IshikawaRasoto/integration-workshop-3/electronics/kicad-5/documentation/aht10_breakout/images/footprint.png

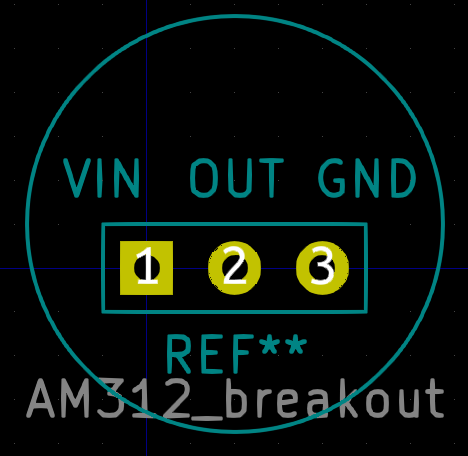
electronics/kicad-5/documentation/aht10_breakout/images/footprint.png
