IshikawaRasoto/integration-workshop-3/electronics/kicad-5/documentation/esp32_devkit_v1_doit/images/3d_top.png

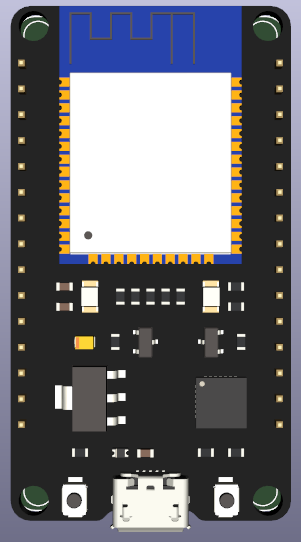
electronics/kicad-5/documentation/esp32_devkit_v1_doit/images/3d_top.png
