IshikawaRasoto/integration-workshop-3/electronics/kicad-5/documentation/esp32_devkit_v1_doit/images/symbol.png

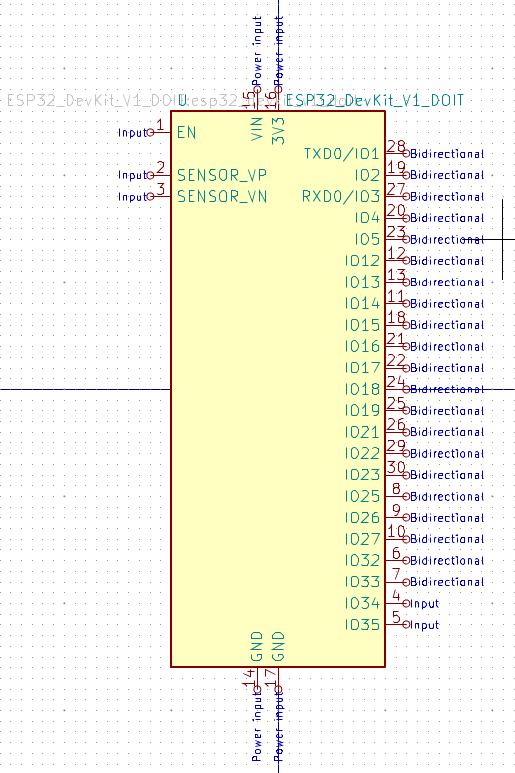
electronics/kicad-5/documentation/esp32_devkit_v1_doit/images/symbol.png
