IshikawaRasoto/integration-workshop-3/electronics/kicad-5/documentation/kf301_5.0/images/3d_view.png

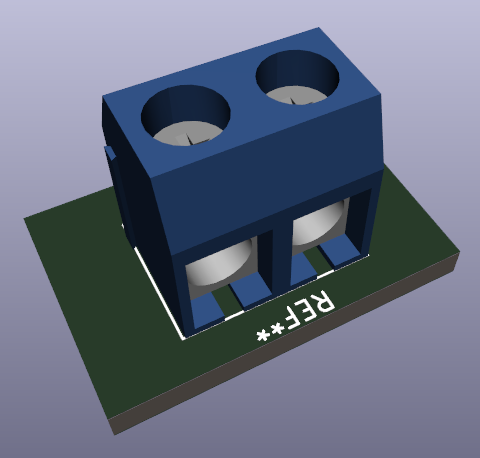
electronics/kicad-5/documentation/kf301_5.0/images/3d_view.png
