IshikawaRasoto/integration-workshop-3/electronics/kicad-5/documentation/kf301_5.0/images/picture.jpg

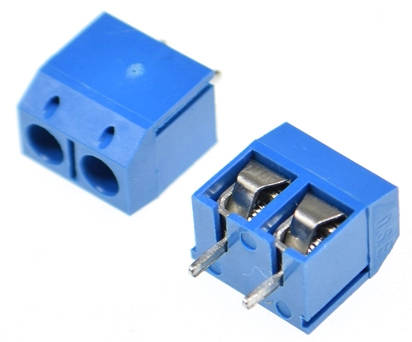
electronics/kicad-5/documentation/kf301_5.0/images/picture.jpg
