IshikawaRasoto/integration-workshop-3/electronics/melody/melody.kicad_pcb

## KiCad design electronics/melody/melody.kicad_pcb (2025-05-14)

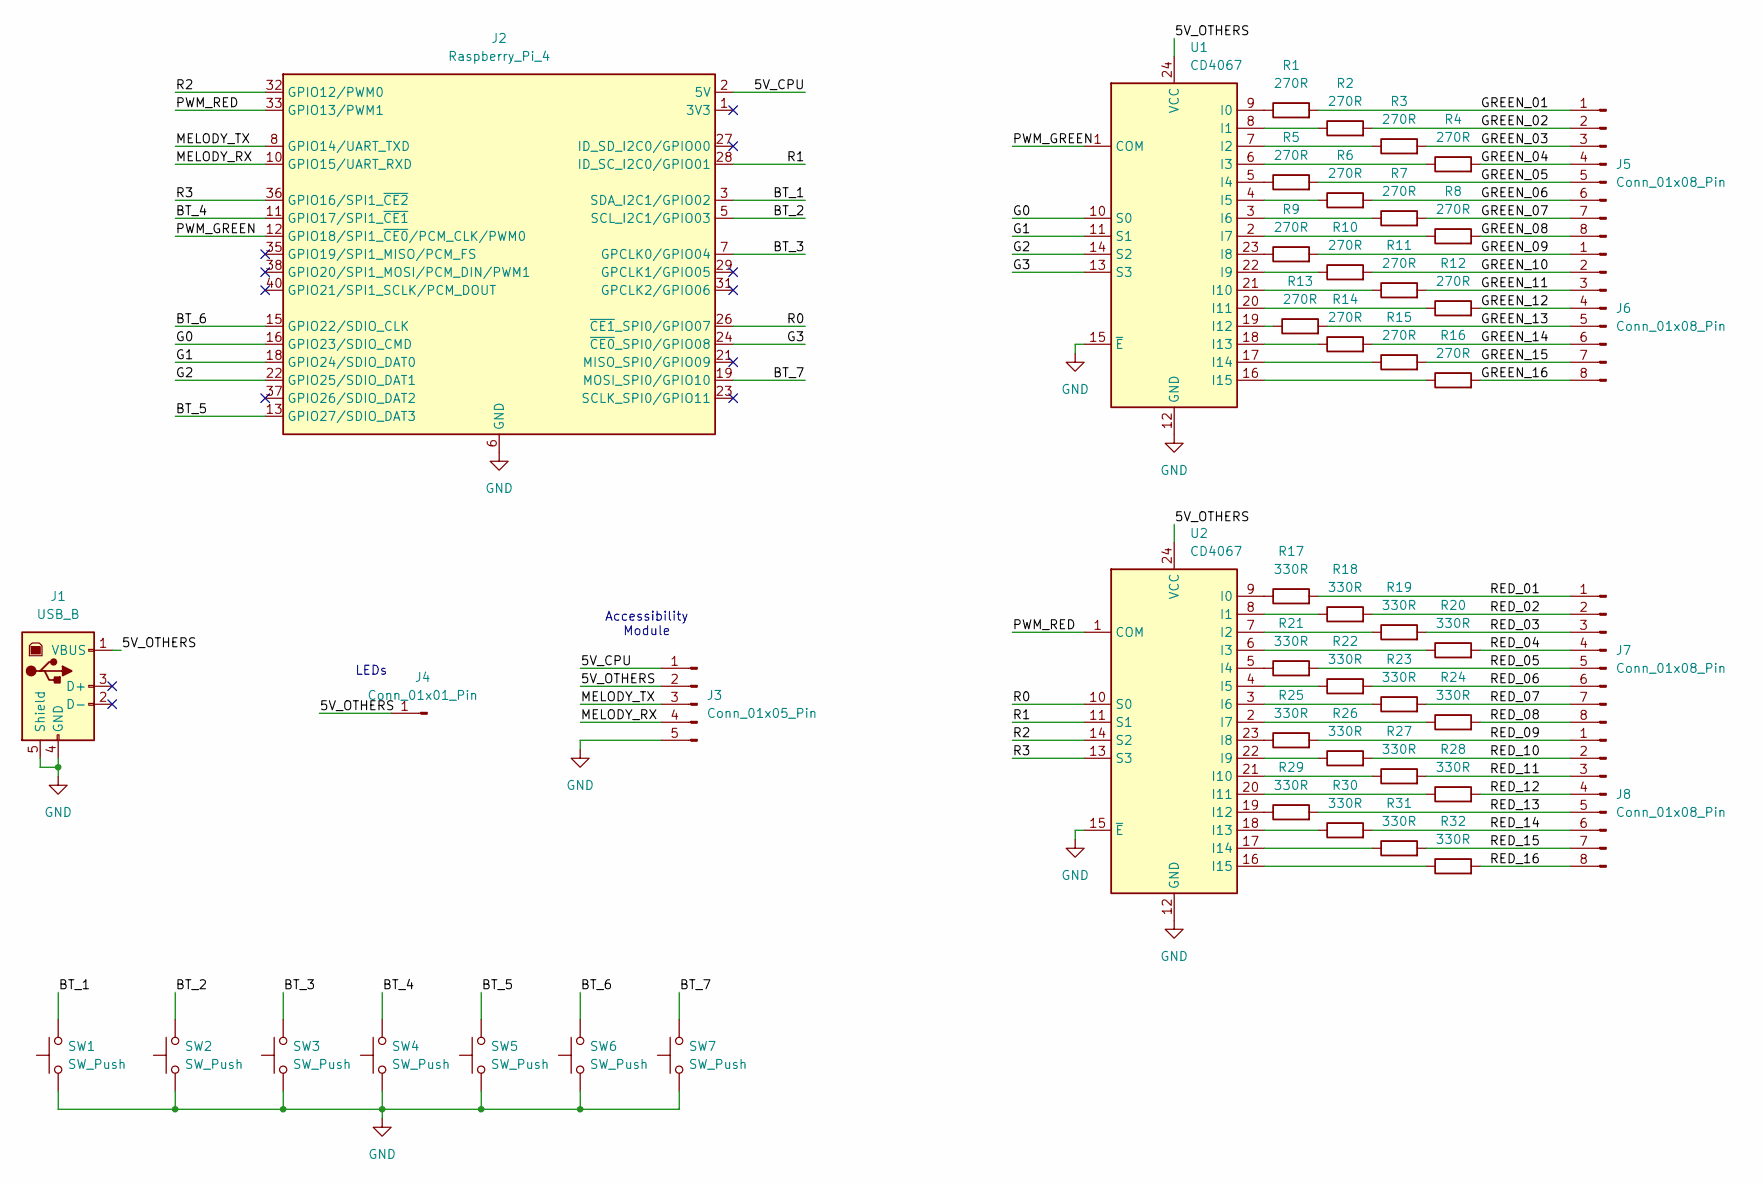
[picture p17: schematic melody.kicad_sch]

Parts:
J1: USB_B; USB_B_TE_5787834_Vertical
J2: Raspberry_Pi_4; PinSocket_2x20_P2.54mm_Vertical
J3: Conn_01x05_Pin; PinHeader_1x05_P2.54mm_Vertical
J4: Conn_01x01_Pin; PinSocket_1x01_P2.54mm_Vertical
J5, J6, J7, J8: Conn_01x08_Pin; PinHeader_1x08_P2.54mm_Vertical
R1, R2, R3, R4, R5, R6, R7, R8, R9, R10, R11, R12, R13, R14, R15, R16: 270R; R_Axial_DIN0204_L3.6mm_D1.6mm_P7.62mm_Horizontal
R17, R18, R19, R20, R21, R22, R23, R24, R25, R26, R27, R28, R29, R30, R31, R32: 330R; R_Axial_DIN0204_L3.6mm_D1.6mm_P7.62mm_Horizontal
SW1, SW2, SW3, SW4, SW5, SW6, SW7: SW_Push; PinHeader_1x02_P2.54mm_Vertical
U1, U2: CD4067; DIP-24_W15.24mm_LongPads

Connections:
/5V_CPU: J2.2 (5V), J2.4 (5V), J3.1
/5V_OTHERS: J1.1 (VBUS), J3.2, J4.1, U1.24 (VCC), U2.24 (VCC)
/BT_1: J2.3 (SDA_I2C1/GPIO02), SW1.2
/BT_2: J2.5 (SCL_I2C1/GPIO03), SW2.2
/BT_3: J2.7 (GPCLK0/GPIO04), SW3.2
/BT_4: J2.11 (GPIO17/SPI1_~CE1), SW4.2
/BT_5: J2.13 (GPIO27/SDIO_DAT3), SW5.2
/BT_6: J2.15 (GPIO22/SDIO_CLK), SW6.2
/BT_7: J2.19 (MOSI_SPI0/GPIO10), SW7.2
/G0: J2.16 (GPIO23/SDIO_CMD), U1.10 (S0)
/G1: J2.18 (GPIO24/SDIO_DAT0), U1.11 (S1)
/G2: J2.22 (GPIO25/SDIO_DAT1), U1.14 (S2)
/G3: J2.24 (~CE0_SPI0/GPIO08), U1.13 (S3)
/GREEN_01: J5.1, R1.2
/GREEN_02: J5.2, R2.2
/GREEN_03: J5.3, R3.2
/GREEN_04: J5.4, R4.2
/GREEN_05: J5.5, R5.2
/GREEN_06: J5.6, R6.2
/GREEN_07: J5.7, R7.2
/GREEN_08: J5.8, R8.2
/GREEN_09: J6.1, R9.2
/GREEN_10: J6.2, R10.2
/GREEN_11: J6.3, R11.2
/GREEN_12: J6.4, R12.2
/GREEN_13: J6.5, R13.2
/GREEN_14: J6.6, R14.2
/GREEN_15: J6.7, R15.2
/GREEN_16: J6.8, R16.2
/MELODY_RX: J2.10 (GPIO15/UART_RXD), J3.4
/MELODY_TX: J2.8 (GPIO14/UART_TXD), J3.3
/PWM_GREEN: J2.12 (GPIO18/SPI1_~CE0/PCM_CLK/PWM0), U1.1 (COM)
/PWM_RED: J2.33 (GPIO13/PWM1), U2.1 (COM)
/R0: J2.26 (~CE1_SPI0/GPIO07), U2.10 (S0)
/R1: J2.28 (ID_SC_I2C0/GPIO01), U2.11 (S1)
/R2: J2.32 (GPIO12/PWM0), U2.14 (S2)
/R3: J2.36 (GPIO16/SPI1_~CE2), U2.13 (S3)
/RED_01: J7.1, R17.2
/RED_02: J7.2, R18.2
/RED_03: J7.3, R19.2
/RED_04: J7.4, R20.2
/RED_05: J7.5, R21.2
/RED_06: J7.6, R22.2
/RED_07: J7.7, R23.2
/RED_08: J7.8, R24.2
/RED_09: J8.1, R25.2
/RED_10: J8.2, R26.2
/RED_11: J8.3, R27.2
/RED_12: J8.4, R28.2
/RED_13: J8.5, R29.2
/RED_14: J8.6, R30.2
/RED_15: J8.7, R31.2
/RED_16: J8.8, R32.2
GND: J1.4 (GND), J1.5 (Shield), J2.6 (GND), J2.9 (GND), J2.14 (GND), J2.20 (GND), J2.25 (GND), J2.30 (GND), J2.34 (GND), J2.39 (GND), J3.5, SW1.1, SW2.1, SW3.1, SW4.1, SW5.1, SW6.1, SW7.1, U1.12 (GND), U1.15 (~E), U2.12 (GND), U2.15 (~E)
unnamed: R1.1, U1.9 (I0)
unnamed: R2.1, U1.8 (I1)
unnamed: R3.1, U1.7 (I2)
unnamed: R4.1, U1.6 (I3)
unnamed: R5.1, U1.5 (I4)
unnamed: R6.1, U1.4 (I5)
unnamed: R7.1, U1.3 (I6)
unnamed: R8.1, U1.2 (I7)
unnamed: R9.1, U1.23 (I8)
unnamed: R10.1, U1.22 (I9)
unnamed: R11.1, U1.21 (I10)
unnamed: R12.1, U1.20 (I11)
unnamed: R13.1, U1.19 (I12)
unnamed: R14.1, U1.18 (I13)
unnamed: R15.1, U1.17 (I14)
unnamed: R16.1, U1.16 (I15)
unnamed: R17.1, U2.9 (I0)
unnamed: R18.1, U2.8 (I1)
unnamed: R19.1, U2.7 (I2)
unnamed: R20.1, U2.6 (I3)
unnamed: R21.1, U2.5 (I4)
unnamed: R22.1, U2.4 (I5)
unnamed: R23.1, U2.3 (I6)
unnamed: R24.1, U2.2 (I7)
unnamed: R25.1, U2.23 (I8)
unnamed: R26.1, U2.22 (I9)
unnamed: R27.1, U2.21 (I10)
unnamed: R28.1, U2.20 (I11)
unnamed: R29.1, U2.19 (I12)
unnamed: R30.1, U2.18 (I13)
unnamed: R31.1, U2.17 (I14)
unnamed: R32.1, U2.16 (I15)

Notes on the sheet:
LEDs
Accessibility Module

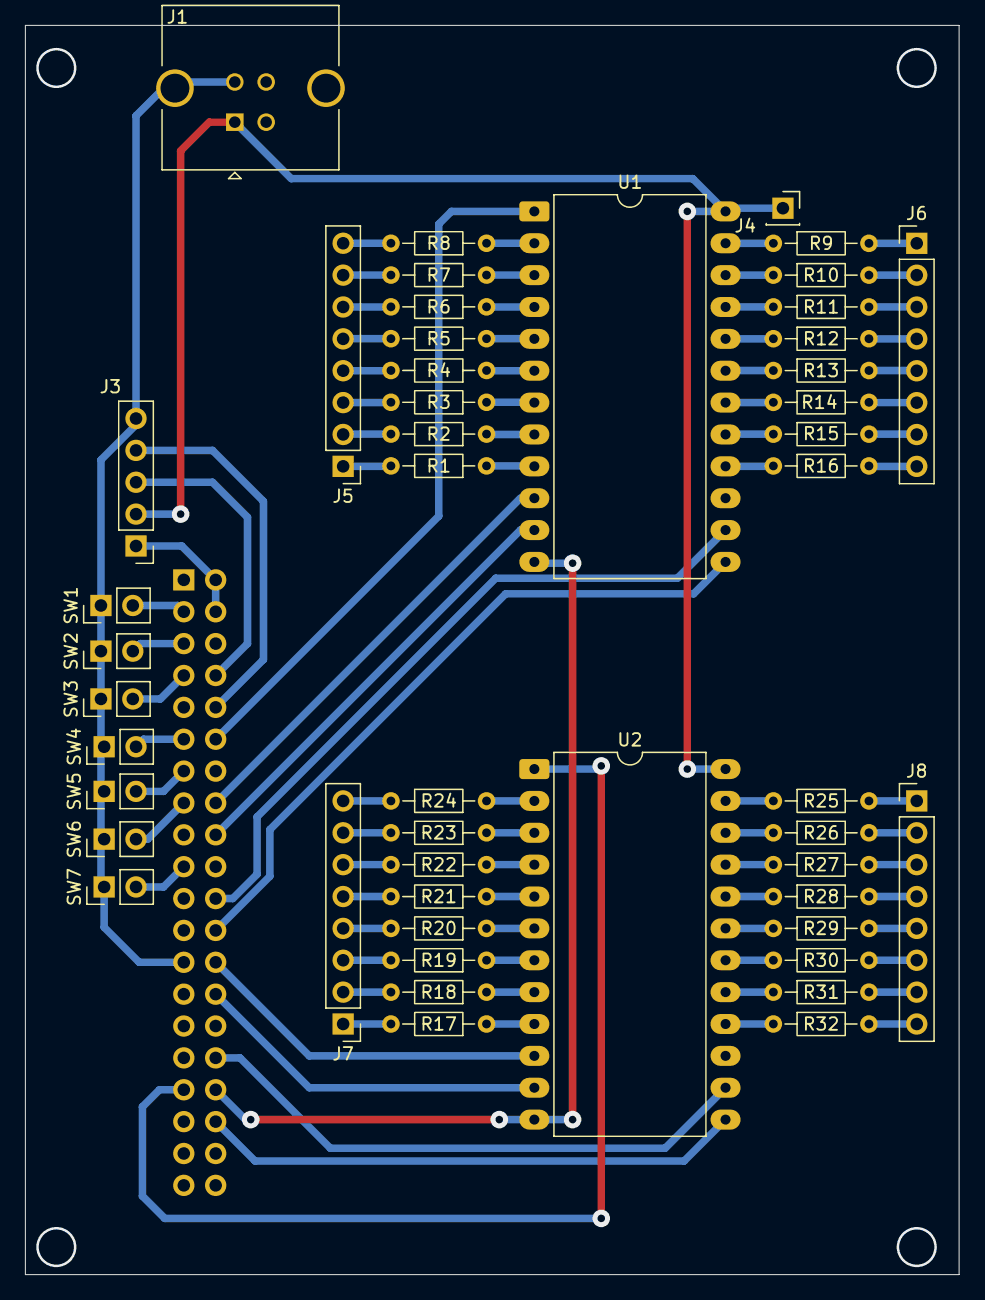
[picture p18: board melody.kicad_pcb from above]

Board: 2 copper layers, 74.4 x 99.6 mm, 49 parts (1 on the bottom side), 86 nets.
