IshikawaRasoto/integration-workshop-3/electronics/accessibility_module/accessibility_module.kicad_pcb

## KiCad design electronics/accessibility_module/accessibility_module.kicad_pcb (2025-05-14)

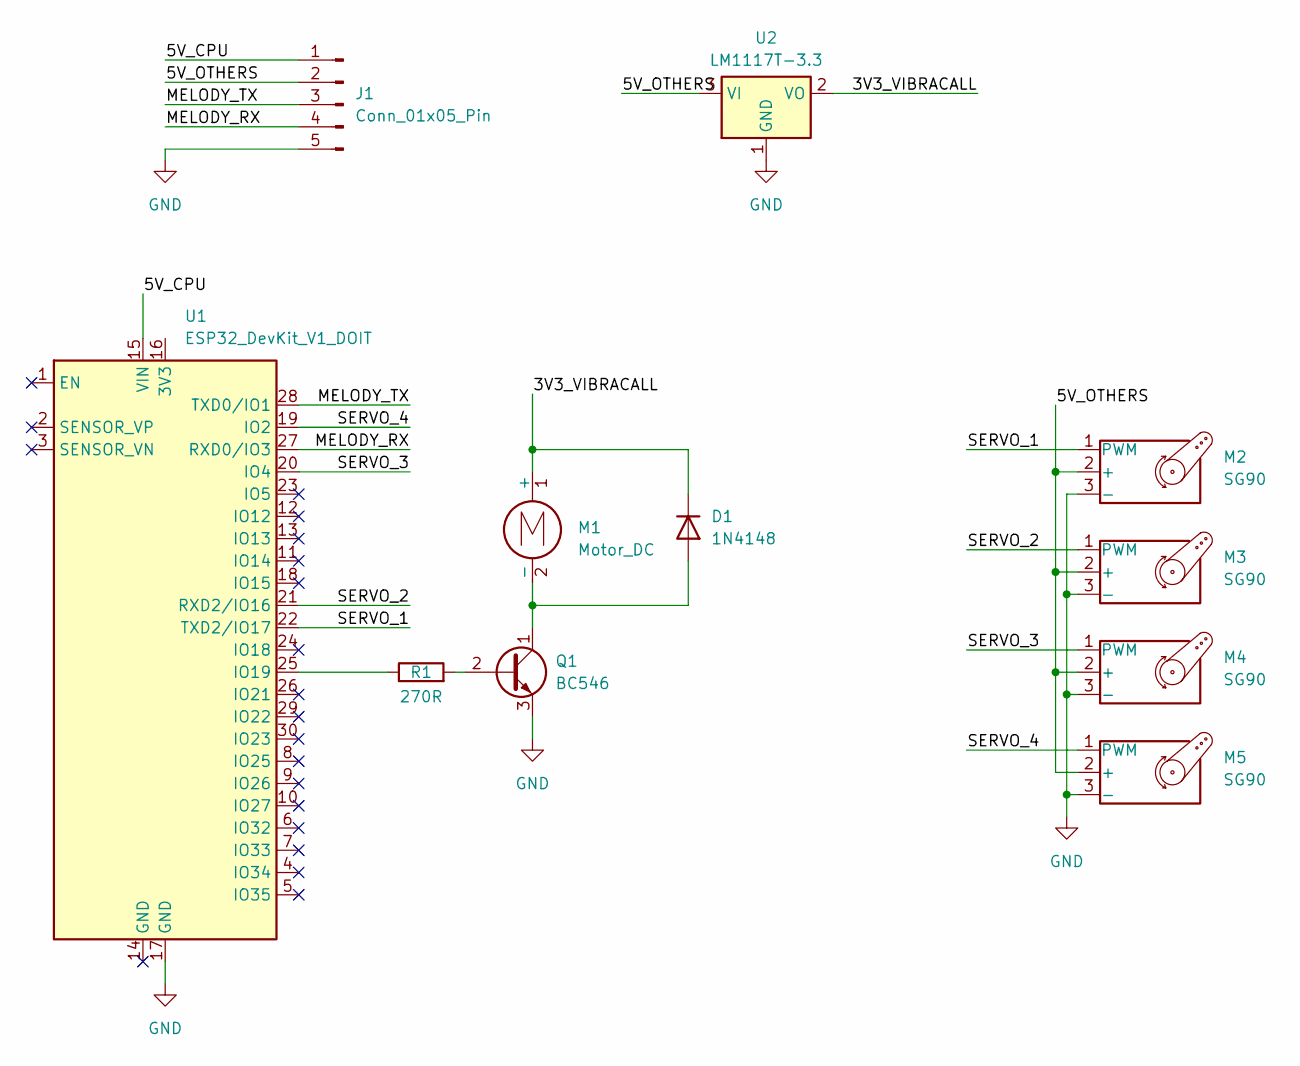
[picture p19: schematic accessibility_module.kicad_sch, Accessibility Module]

Parts:
D1: 1N4148; D_DO-35_SOD27_P7.62mm_Horizontal
J1: Conn_01x05_Pin; PinHeader_1x05_P2.54mm_Vertical
M1: Motor_DC; PinHeader_1x02_P2.54mm_Vertical
M2, M3, M4, M5: SG90; PinHeader_1x03_P2.54mm_Vertical
Q1: BC546; TO-92_Inline
R1: 270R; R_Axial_DIN0204_L3.6mm_D1.6mm_P7.62mm_Horizontal
U1: ESP32_DevKit_V1_DOIT; esp32_devkit_v1_doit
U2: LM1117T-3.3; TO-220-3_Vertical

Connections:
/3V3_VIBRACALL: D1.1 (K), M1.1 (+), U2.2 (VO)
/5V_CPU: J1.1, U1.15 (VIN)
/5V_OTHERS: J1.2, M2.2 (+), M3.2 (+), M4.2 (+), M5.2 (+), U2.3 (VI)
/MELODY_RX: J1.4, U1.27 (RXD0/IO3)
/MELODY_TX: J1.3, U1.28 (TXD0/IO1)
/SERVO_1: M2.1 (PWM), U1.22 (TXD2/IO17)
/SERVO_2: M3.1 (PWM), U1.21 (RXD2/IO16)
/SERVO_3: M4.1 (PWM), U1.20 (IO4)
/SERVO_4: M5.1 (PWM), U1.19 (IO2)
GND: J1.5, M2.3 (-), M3.3 (-), M4.3 (-), M5.3 (-), Q1.3 (E), U1.17 (GND), U2.1 (GND)
unnamed: D1.2 (A), M1.2 (-), Q1.1 (C)
unnamed: Q1.2 (B), R1.2
unnamed: R1.1, U1.25 (IO19)

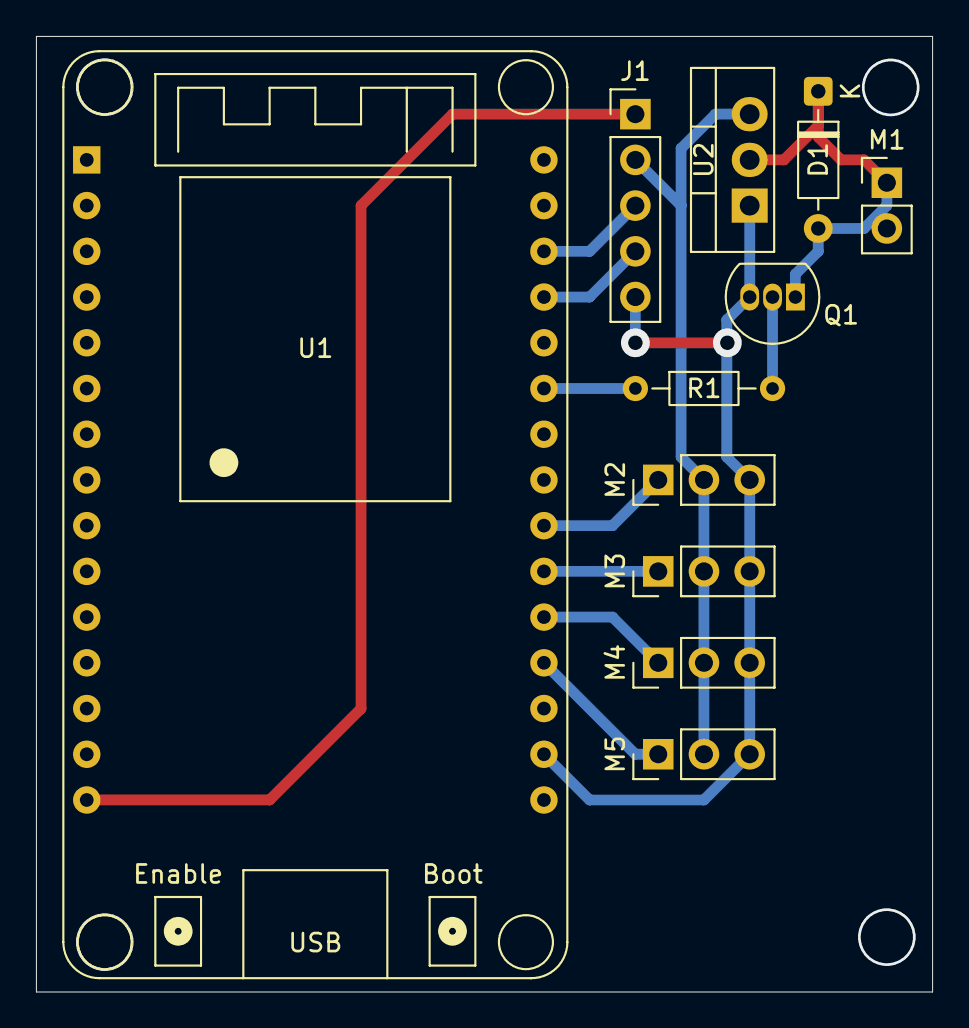
[picture p20: board accessibility_module.kicad_pcb from above]

Board: 2 copper layers, 49.8 x 53.1 mm, 11 parts (0 on the bottom side), 13 nets.
