IshikawaRasoto/integration-workshop-3/backend/core/utils.py

# Melodies

ODE_ALEGRIA = [
    ("C5#", "quarter"), ("C5#", "quarter"), ("D5", "quarter"), ("E5", "quarter"),
    ("E5", "quarter"), ("D5", "quarter"), ("C5#", "quarter"), ("B4", "quarter"),
    ("A4", "half"), ("R", ""), ("B4", "quarter"), ("C5#", "quarter"),
    ("C5#", "half"), ("R", ""), ("B4", "half"), ("R", "")

]

CANON_IN_D = [
    ("D5", "half"), ("R", ""), ("A4", "half"), ("R", ""),
    ("B4", "half"), ("R", ""), ("F4#", "half"), ("R", ""),
    ("G4", "half"), ("R", ""), ("D4", "half"), ("R", ""),
    ("G4", "half"), ("R", ""), ("A4", "half"), ("R", "")
]

OVELHA_PRETA = [
    ("G4", "quarter"), ("G4", "quarter"), ("D5", "quarter"), ("D5", "quarter"),
    ("E5", "quarter"), ("E5", "quarter"), ("D5", "half"),    ("R", ""),
    ("C5", "quarter"), ("C5", "quarter"), ("B4", "quarter"), ("B4", "quarter"),
    ("A4", "quarter"), ("A4", "quarter"), ("G4", "half"),    ("R", "")
]


# Frequencies for 12 chromatic notes
note_freqs = {
    'C1': 32.70, 'C1#': 34.65, 'D1b': 34.65, 'D1': 36.71, 'D1#': 38.89, 'E1b': 38.89, 'E1': 41.20,
    'F1': 43.65, 'F1#': 46.25, 'G1b': 46.25, 'G1': 49.00, 'G1#': 51.91, 'A1b': 51.91, 'A1': 55.00,
    'A1#': 58.27, 'B1b': 58.27, 'B1': 61.74,
    'C2': 65.41, 'C2#': 69.30, 'D2b': 69.30, 'D2': 73.42, 'D2#': 77.78, 'E2b': 77.78, 'E2': 82.41,
    'F2': 87.31, 'F2#': 92.50, 'G2b': 92.50, 'G2': 98.00, 'G2#': 103.83, 'A2b': 103.83, 'A2': 110.00,
    'A2#': 116.54, 'B2b': 116.54, 'B2': 123.47,
    'C3': 130.81, 'C3#': 138.59, 'D3b': 138.59, 'D3': 146.83, 'D3#': 155.56, 'E3b': 155.56, 'E3': 164.81,
    'F3': 174.61, 'F3#': 185.00, 'G3b': 185.00, 'G3': 196.00, 'G3#': 207.65, 'A3b': 207.65, 'A3': 220.00,
    'A3#': 233.08, 'B3b': 233.08, 'B3': 246.94,
    'C4': 261.63, 'C4#': 277.18, 'D4b': 277.18, 'D4': 293.66, 'D4#': 311.13, 'E4b': 311.13, 'E4': 329.63,
    'F4': 349.23, 'F4#': 369.99, 'G4b': 369.99, 'G4': 392.00, 'G4#': 415.30, 'A4b': 415.30, 'A4': 440.00,
    'A4#': 466.16, 'B4b': 466.16, 'B4': 493.88,
    'C5': 523.25, 'C5#': 554.37, 'D5b': 554.37, 'D5': 587.33, 'D5#': 622.25, 'E5b': 622.25, 'E5': 659.25,
    'F5': 698.46, 'F5#': 739.99, 'G5b': 739.99, 'G5': 783.99, 'G5#': 830.61, 'A5b': 830.61, 'A5': 880.00,
    'A5#': 932.33, 'B5b': 932.33, 'B5': 987.77,
    'C6': 1046.50, 'C6#': 1108.73, 'D6b': 1108.73, 'D6': 1174.66, 'D6#': 1244.51, 'E6b': 1244.51, 'E6': 1318.51,
    'F6': 1396.91, 'F6#': 1479.98, 'G6b': 1479.98, 'G6': 1567.98, 'G6#': 1661.22, 'A6b': 1661.22, 'A6': 1760.00,
    'A6#': 1864.66, 'B6b': 1864.66, 'B6': 1975.53,
    'R': None,
    'None': None
}
